rerebebekkkkaaaa/BexxiGun/TVbGoneCodes.h

const int codes_eu[] PROGMEM= {
   35714, 80, 0 ,
   30303, 62, 80 ,
   33333, 52, 142 ,
   38400, 52, 194 ,
   37037, 200, 246 ,
   38610, 128, 446 ,
   38462, 136, 574 ,
   38462, 104, 710 ,
   38462, 76, 814 ,
   35714, 48, 890 ,
   38610, 76, 938 ,
   38462, 76, 1014 ,
   33445, 52, 1090 ,
   38462, 176, 1142 ,
   38462, 76, 1318 ,
   38462, 272, 1394 ,
   33333, 68, 1666 ,
   33333, 48, 1734 ,
   38462, 76, 1782 ,
   38462, 76, 1858 ,
   35714, 68, 1934 ,
   38462, 76, 2002 ,
   38462, 76, 2078 ,
   38462, 76, 2154 ,
   38462, 76, 2230 ,
   31250, 42, 2306 ,
   38462, 48, 2348 ,
   38462, 76, 2396 ,
   30303, 62, 2472 ,
   34483, 92, 2534 ,
   38462, 76, 2626 ,
   38462, 104, 2702 ,
   33333, 52, 2806 ,
   38462, 28, 2858 ,
   38462, 76, 2886 ,
   38462, 76, 2962 ,
   38462, 48, 3038 ,
   0, 22, 3086 ,
   40161, 48, 3108 ,
   35714, 104, 3156 ,
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
  };

const unsigned short codes2_eu[] PROGMEM= {
264,90,43,91,43,47,43,47,133,133,43,47,43,47,43,47,43,47,43,47,43,47,43,47,43,47,43,47,43,47,43,47,
  88,47,43,91,43,47,43,8324,264,91,43,91,43,47,43,47,133,133,43,47,43,47,43,47,43,47,43,47,43,47,43,47,
  43,47,43,47,43,47,43,47,88,47,43,91,43,47,43,91,47,265,51,54,51,54,51,54,51,54,51,54,51,54,51,54,
  51,54,51,54,51,2053,51,263,51,108,100,109,51,54,51,54,51,54,51,54,51,54,51,54,51,11647,51,263,51,108,100,109,
  51,54,51,54,51,54,51,54,51,54,51,54,51,54,43,206,46,204,46,456,46,456,46,204,46,204,46,204,46,456,46,456,
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
  53,171,53,171,53,171,53,171,53,171,53,171,53,2302,895,449,53,171,53,171,53,59,53,171,53,171,53,171,53,171,53,59,
  53,59,53,59,53,59,53,59,53,59,53,59,53,59,53,171,53,59,53,59,53,59,53,59,53,171,53,171,53,171,53,171,
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
};
